fitch22/JetsonDoorbell/main/isr.c

#include "isr.h"
#include "driver/gpio.h"
#include "freertos/FreeRTOS.h"
#include "freertos/task.h"
#include "global.h"
#include "gpio.h"
#include <stdlib.h>

// Interrupt service routine, called after sending each DMA buffer
bool i2s_write_callback(i2s_chan_handle_t handle, i2s_event_data_t *event,
                        void *user_ctx) {
#ifdef HW_PROFILE
  gpio_set_level(LA0, 1);
  gpio_set_level(LA0, 0);
#endif
  vTaskNotifyGiveFromISR(xFillTask, NULL);

  return true;
}

void button1_isr_handler(void *arg) {
  vTaskNotifyGiveFromISR(xButton1Task, NULL);
  gpio_intr_disable(BUTTON1_PIN);
}

void button2_isr_handler(void *arg) {
  vTaskNotifyGiveFromISR(xButton2Task, NULL);
  gpio_intr_disable(BUTTON2_PIN);
}
